Tonikiller10000/USB-MassStorageDevice/USB_MassStorageDevice_Pictures/20230525_132558.jpg

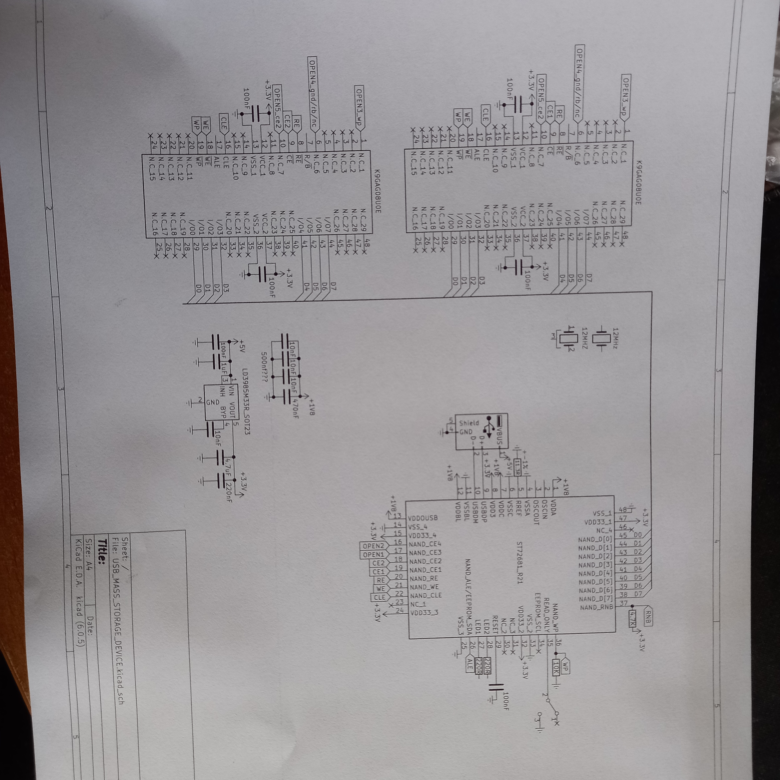
USB_MassStorageDevice_Pictures/20230525_132558.jpg
