Tonikiller10000/USB-MassStorageDevice/USB_MassStorageDevice_Pictures/20231005_144610.jpg

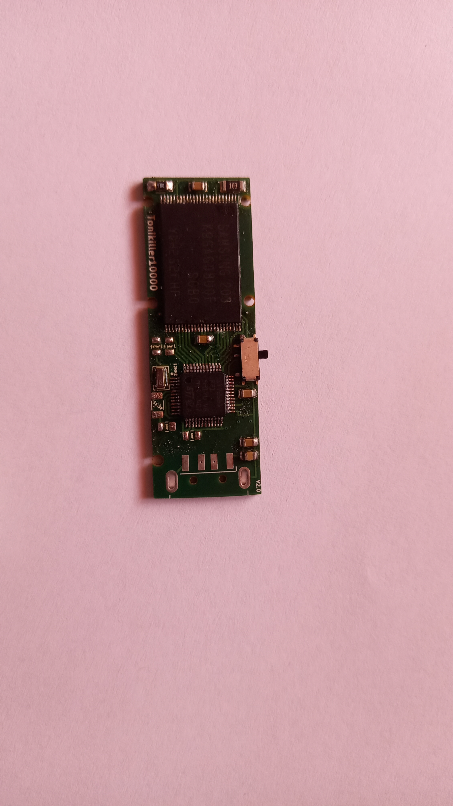
USB_MassStorageDevice_Pictures/20231005_144610.jpg
