Tonikiller10000/USB-MassStorageDevice/USB_MassStorageDevice_Pictures/20231129_174523.jpg

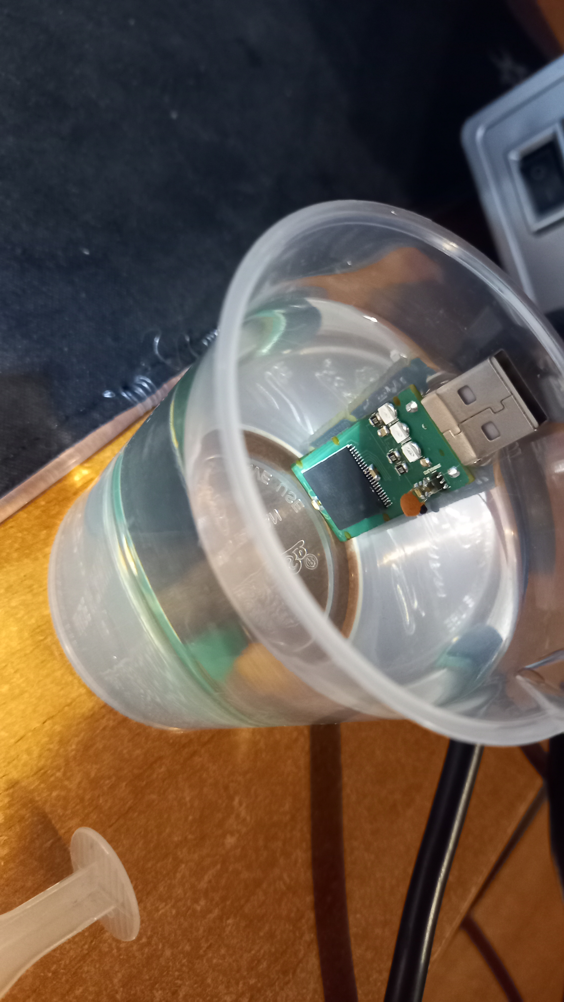
USB_MassStorageDevice_Pictures/20231129_174523.jpg
