Tonikiller10000/USB-MassStorageDevice/USB_MassStorageDevice_Pictures/20231129_174549.jpg

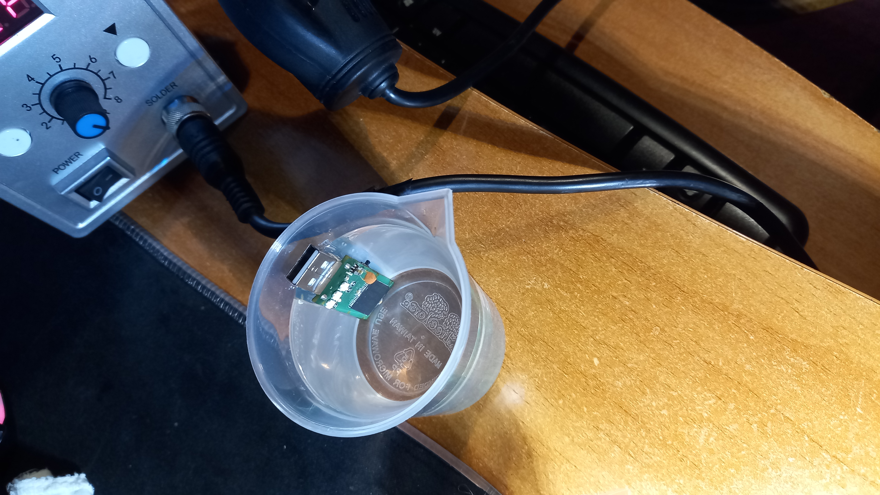
USB_MassStorageDevice_Pictures/20231129_174549.jpg
