Tonikiller10000/USB-MassStorageDevice/USB_MassStorageDevice_Pictures/20231130_201253.jpg

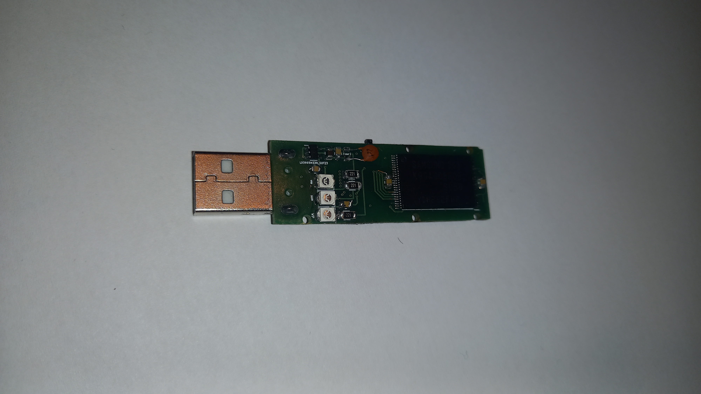
USB_MassStorageDevice_Pictures/20231130_201253.jpg
