Tonikiller10000/USB-MassStorageDevice/USB_MassStorageDevice_Pictures/20231130_201359.jpg

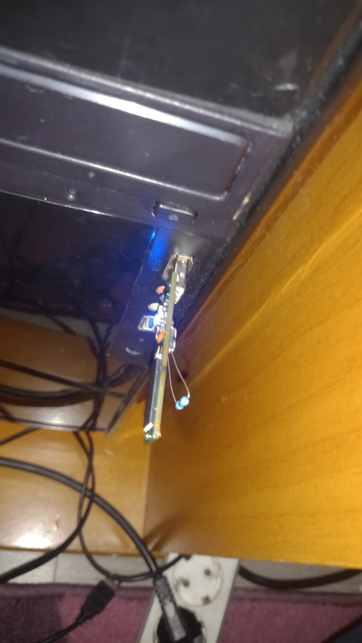
USB_MassStorageDevice_Pictures/20231130_201359.jpg
