Tonikiller10000/USB-MassStorageDevice/USB_MassStorageDevice_Pictures/20231130_201403.jpg

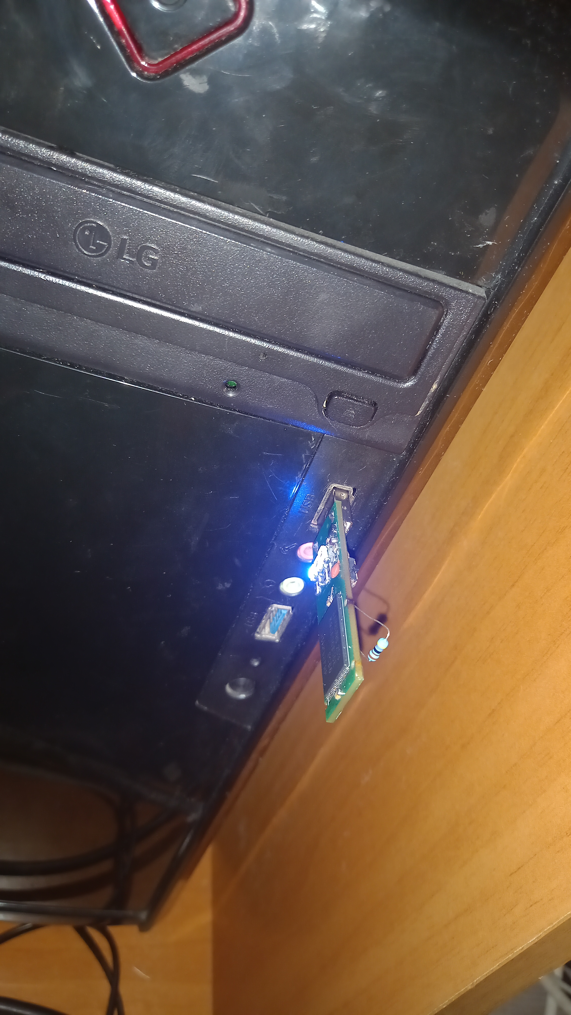
USB_MassStorageDevice_Pictures/20231130_201403.jpg
