Tonikiller10000/USB-MassStorageDevice/USB_MassStorageDevice_Pictures/cleaningD.jpg

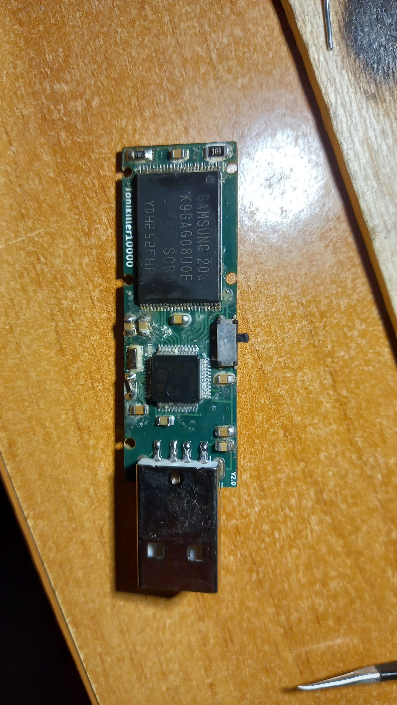
USB_MassStorageDevice_Pictures/cleaningD.jpg
