Tonikiller10000/USB-MassStorageDevice/USB_MassStorageDevice_Pictures/computer1.jpg

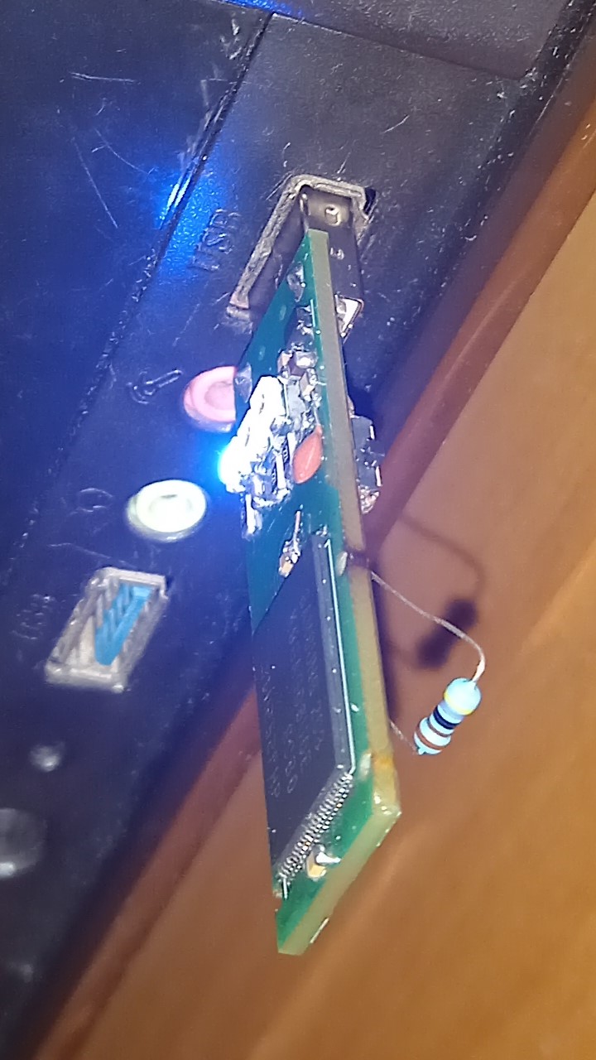
USB_MassStorageDevice_Pictures/computer1.jpg
