Tonikiller10000/USB-MassStorageDevice/USB_MassStorageDevice_Pictures/JLC2.jpg

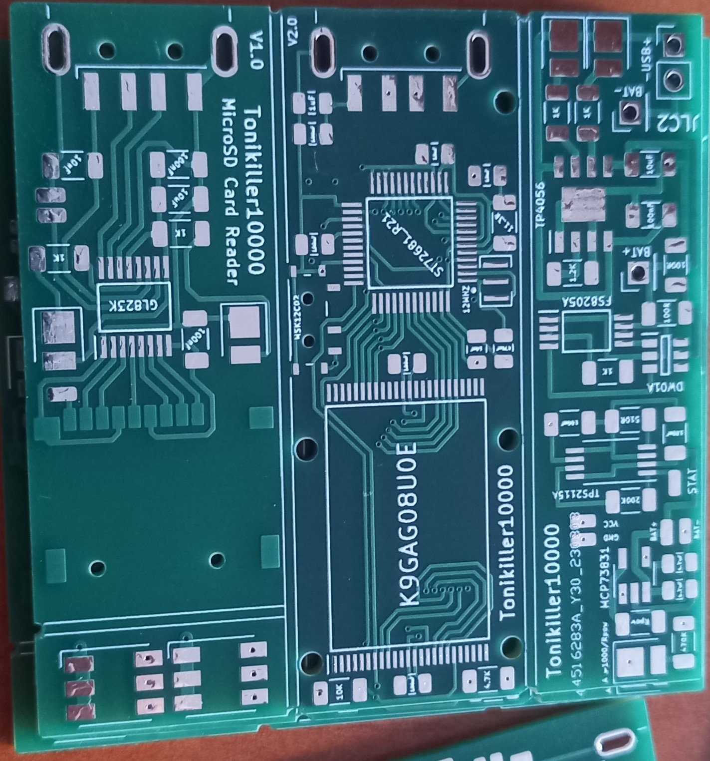
USB_MassStorageDevice_Pictures/JLC2.jpg
