Tonikiller10000/USB-MassStorageDevice/USB_MassStorageDevice_Pictures/JLC2_3D.png

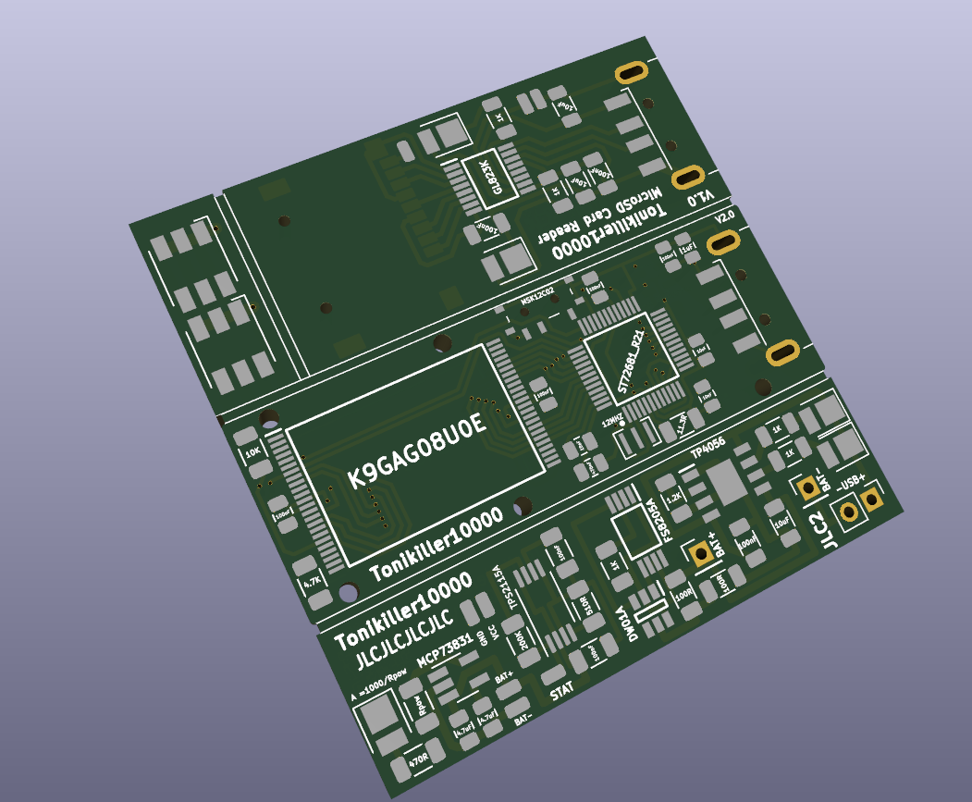
USB_MassStorageDevice_Pictures/JLC2_3D.png
