Tonikiller10000/USB-MassStorageDevice/USB_MassStorageDevice_Pictures/proiectare1.png

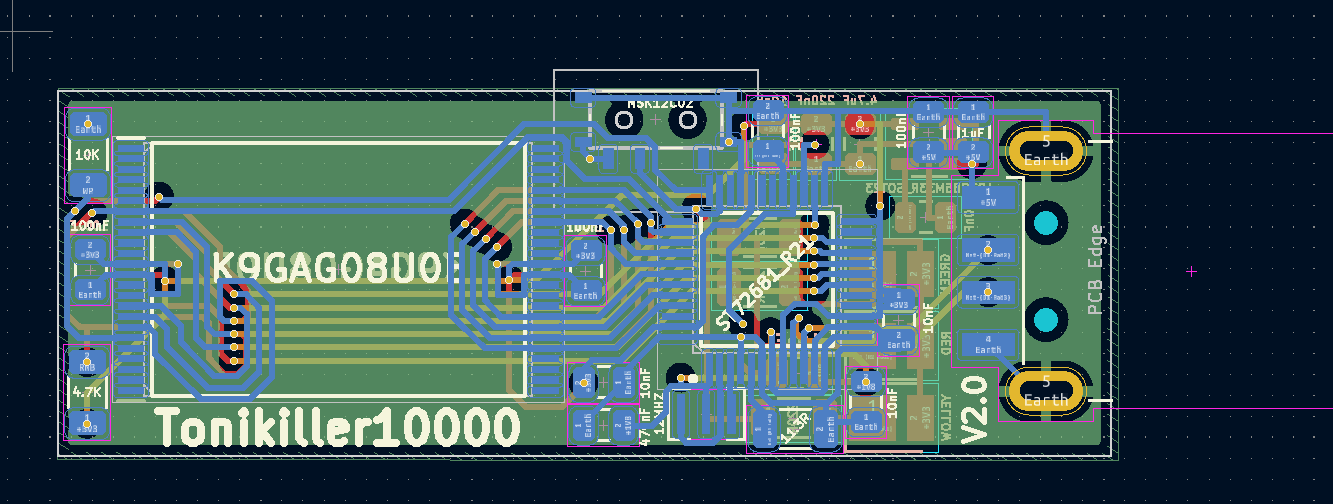
USB_MassStorageDevice_Pictures/proiectare1.png
