Tonikiller10000/USB-MassStorageDevice/USB_MassStorageDevice_Pictures/proiectareV1_1.png

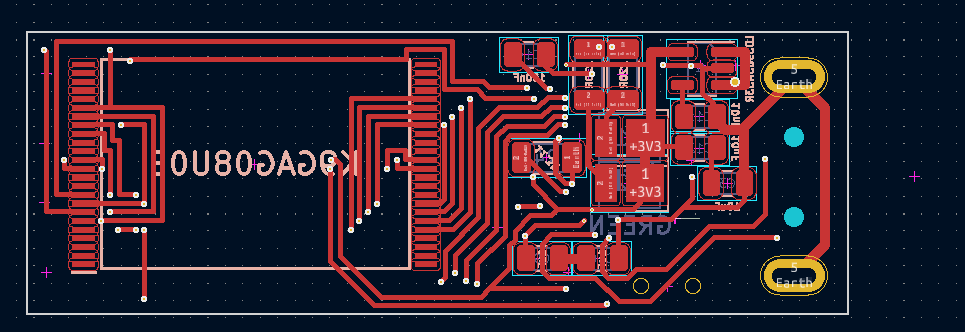
USB_MassStorageDevice_Pictures/proiectareV1_1.png
