Tonikiller10000/USB-MassStorageDevice/USB_MassStorageDevice_Pictures/proiectareV1_2.png

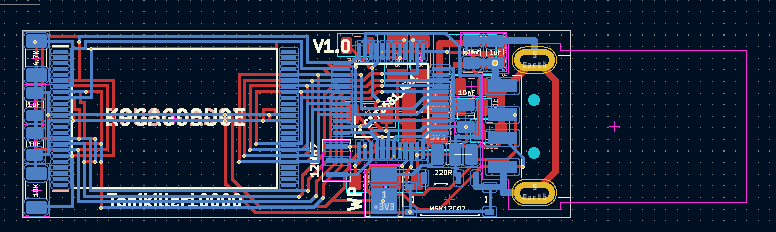
USB_MassStorageDevice_Pictures/proiectareV1_2.png
