Tonikiller10000/USB-MassStorageDevice/USB_MassStorageDevice_Pictures/proiectareV1_3.png

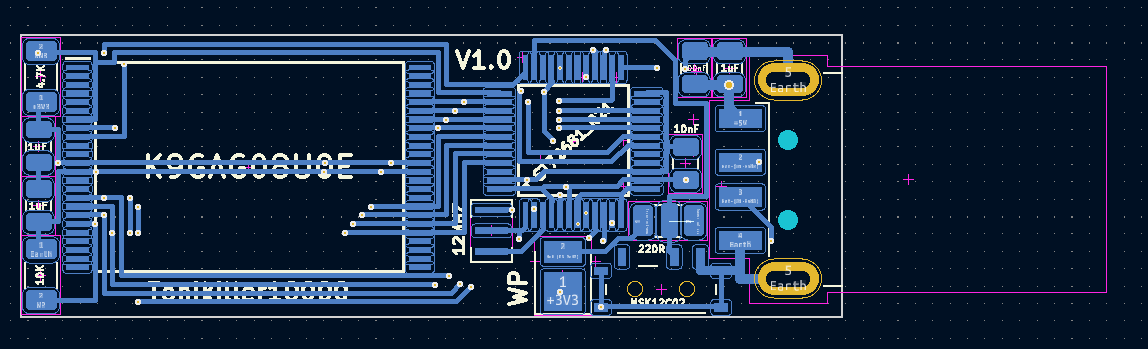
USB_MassStorageDevice_Pictures/proiectareV1_3.png
