Tonikiller10000/USB-MassStorageDevice/USB_MassStorageDevice_Pictures/{63E3E4AF-1289-4379-8FE5-D51F67F114C9}.png

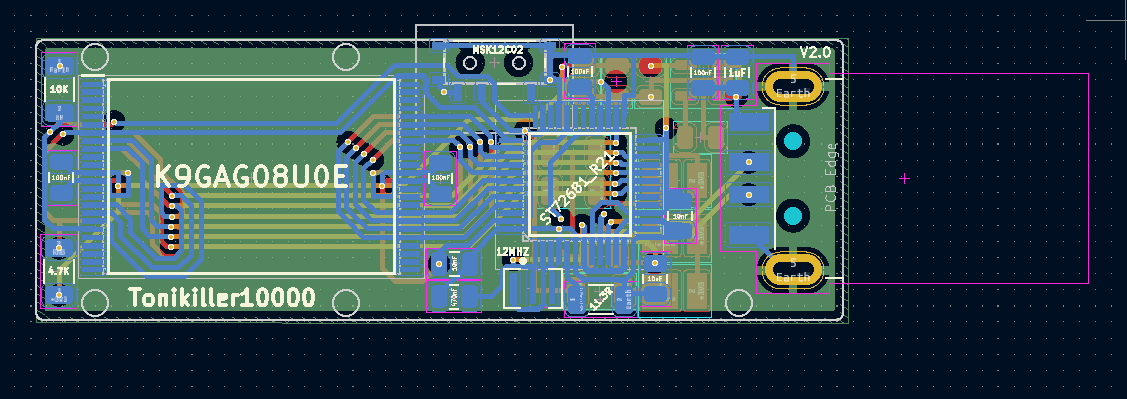
USB_MassStorageDevice_Pictures/{63E3E4AF-1289-4379-8FE5-D51F67F114C9}.png
