Tonikiller10000/USB-MassStorageDevice/USB_MassStorageDevice_Pictures/{971357FA-218E-4658-BFC3-38EEE1B6A8E1}.png

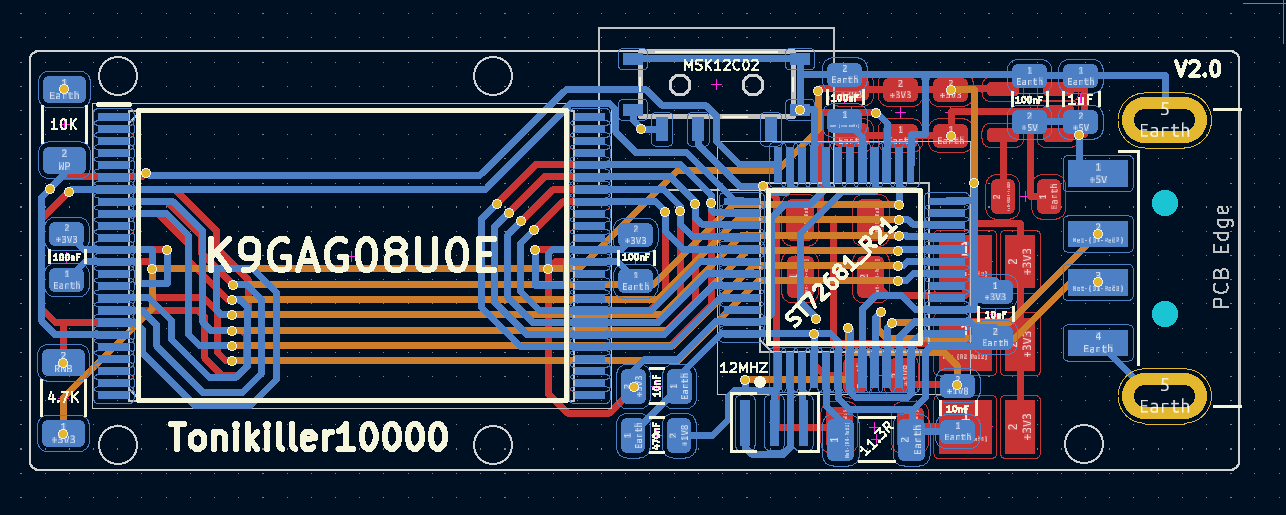
USB_MassStorageDevice_Pictures/{971357FA-218E-4658-BFC3-38EEE1B6A8E1}.png
