Tonikiller10000/USB-MassStorageDevice/USB_MassStorageDevice_Pictures/{18409118-EA69-4E44-BF70-CB54E0C69AAE}.png

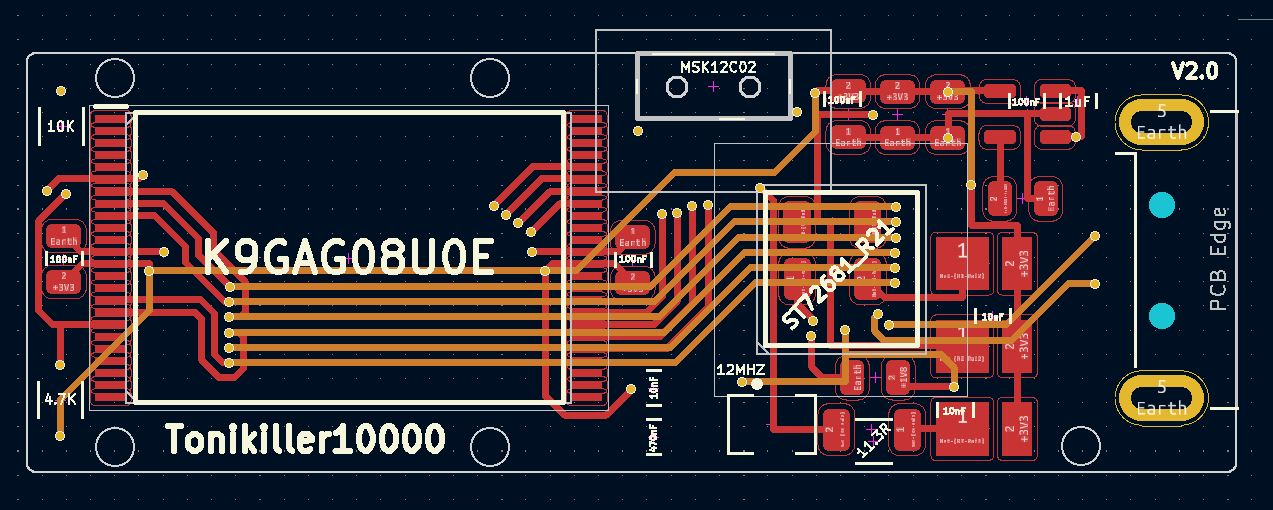
USB_MassStorageDevice_Pictures/{18409118-EA69-4E44-BF70-CB54E0C69AAE}.png
